jackdeath5/CustomPokkenControllerArduinoCode/Images/Pokken Controller No Background (WHITE).png

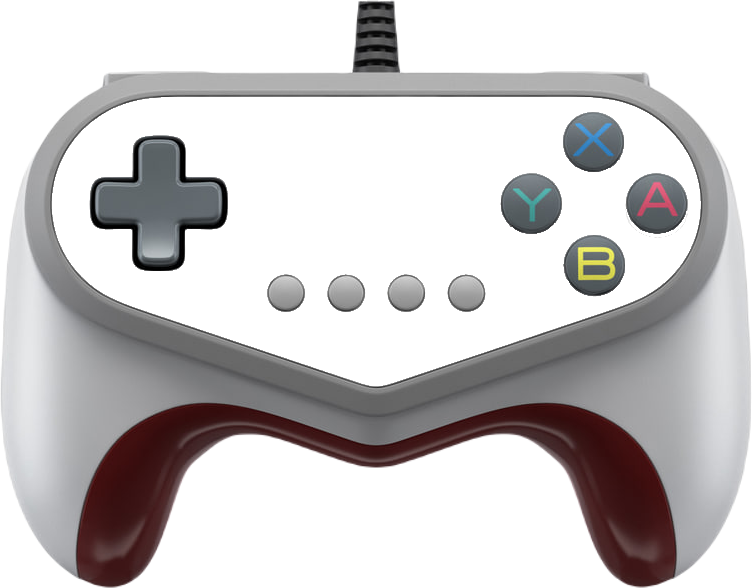
Images/Pokken Controller No Background (WHITE).png
