jackdeath5/CustomPokkenControllerArduinoCode/Images/Usb cable image.jpg

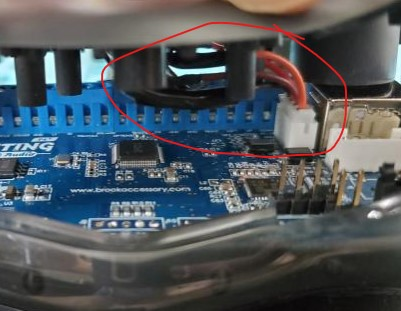
Images/Usb cable image.jpg
